Sysetup/Aluminum-boxes/18 x 29 x 47 cms/Parts/Plates and angles/Connector.FCStd

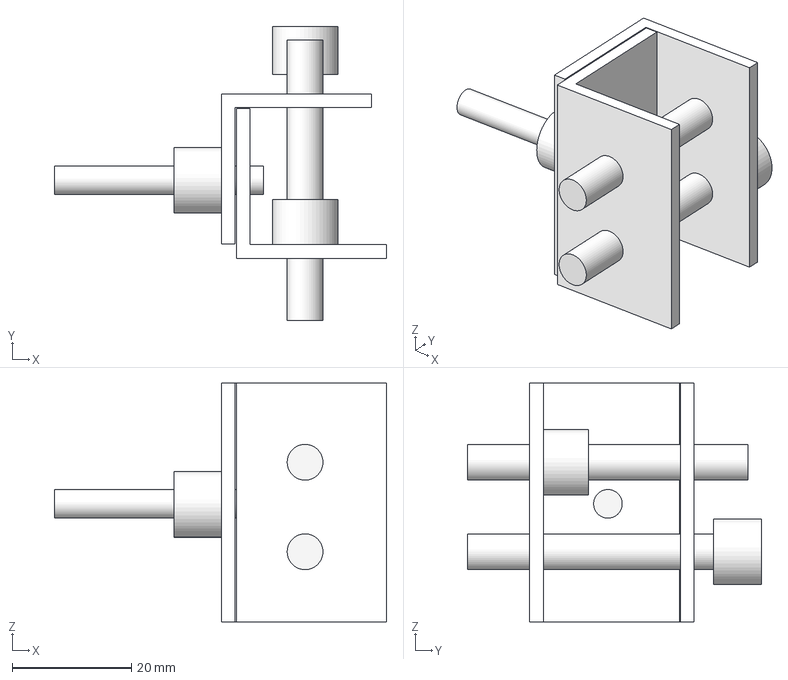
[picture p19: CAD file, 2022-02-21]
18 x 29 x 47 cms/Parts/Plates and angles/Connector.FCStd
55.6 x 49.2 x 40.0 mm
Thickness021
