Sysetup/Aluminum-boxes/18x29x47cms/Parts/Covers/Bottom cover.FCStd

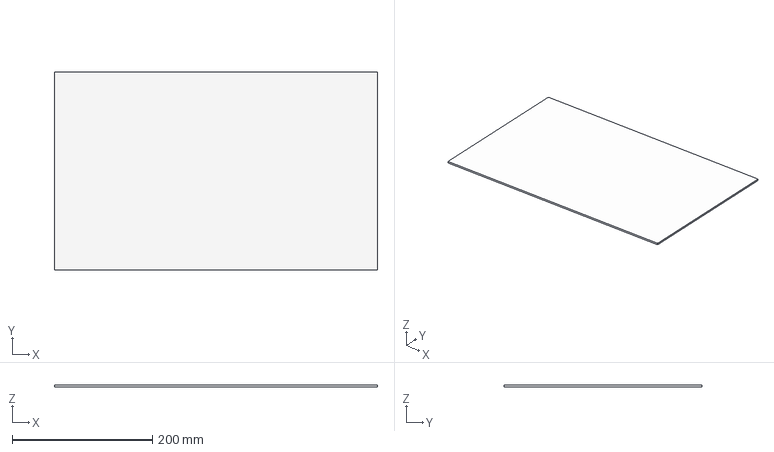
[picture p20: CAD file, 2022-03-06]
18x29x47cms/Parts/Covers/Bottom cover.FCStd
460.0 x 282.0 x 3.00 mm
