Sysetup/Aluminum-boxes/29x29x47cms/Parts/Covers/#21 Left cover.FCStd

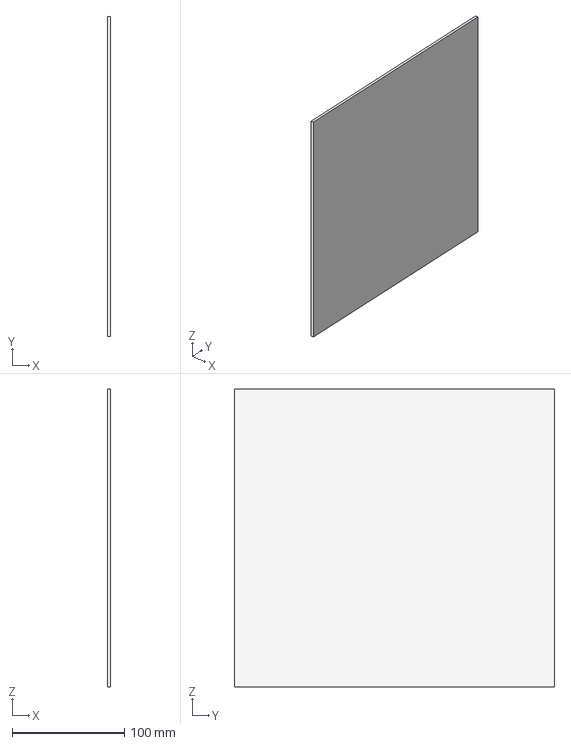
[picture p21: CAD file, 2022-01-28]
29x29x47cms/Parts/Covers/#21 Left cover.FCStd
3.00 x 285.0 x 265.0 mm
