Sysetup/Aluminum-boxes/18x29x47cms/Parts/Covers/Top cover.FCStd

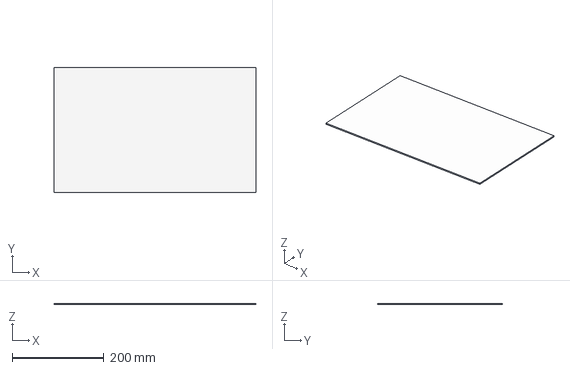
[picture p22: CAD file, 2022-03-06]
18x29x47cms/Parts/Covers/Top cover.FCStd
441.0 x 272.0 x 3.00 mm
