Sysetup/Aluminum-boxes/18 x 29 x 47 cms/Parts/Covers/Left cover.FCStd

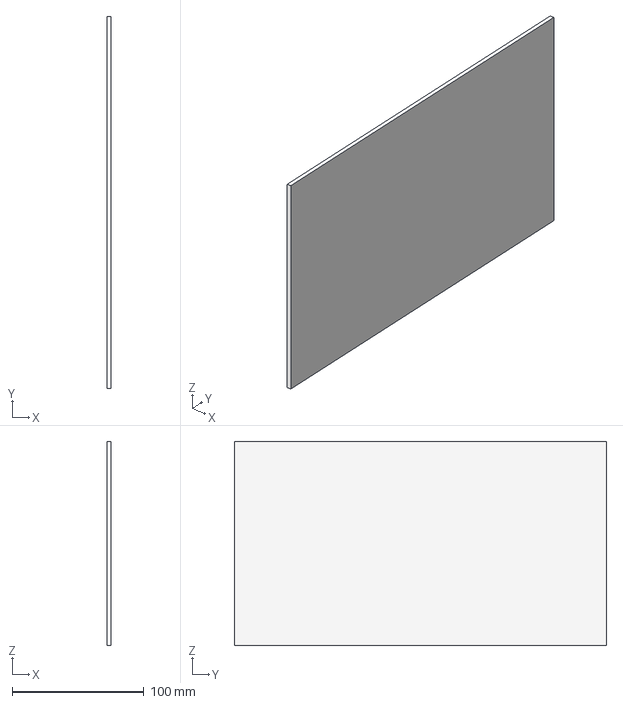
[picture p23: CAD file, 2022-03-06]
18 x 29 x 47 cms/Parts/Covers/Left cover.FCStd
3.00 x 282.0 x 155.0 mm
