Sysetup/Aluminum-boxes/29x29x47cms/Parts/Covers/#17 Front cover.FCStd

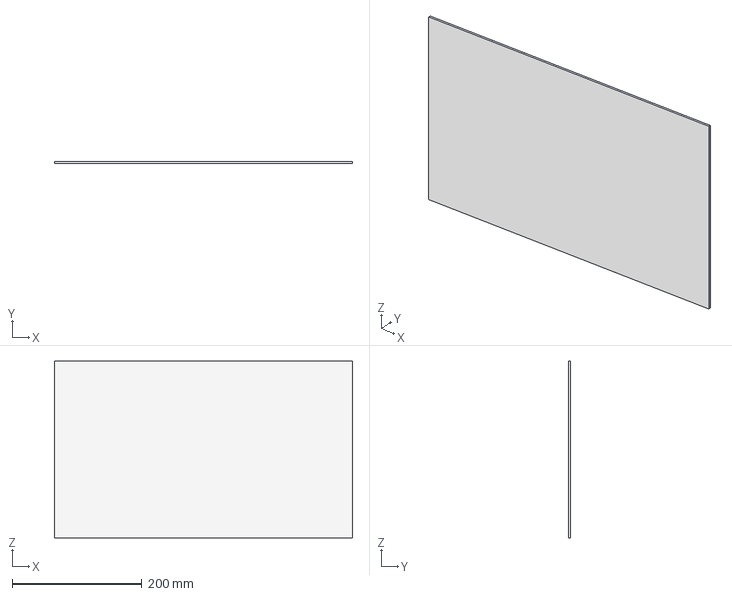
[picture p24: CAD file, 2022-01-28]
29x29x47cms/Parts/Covers/#17 Front cover.FCStd
460.0 x 3.00 x 273.0 mm
