Sysetup/Aluminum-boxes/18 x 29 x 47 cms/Parts/Covers/Alfajor.FCStd

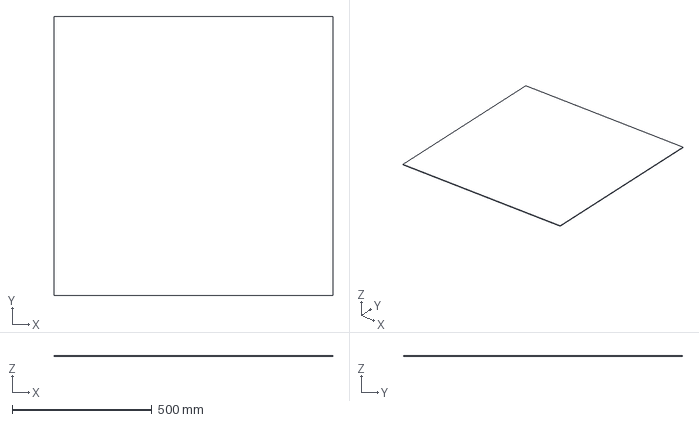
[picture p25: CAD file, 2022-03-06]
18 x 29 x 47 cms/Parts/Covers/Alfajor.FCStd
1000.0 x 1000.0 x 3.00 mm
