Sysetup/Aluminum-boxes/29x29x47cms/Parts/Covers/#18 Top cover.FCStd

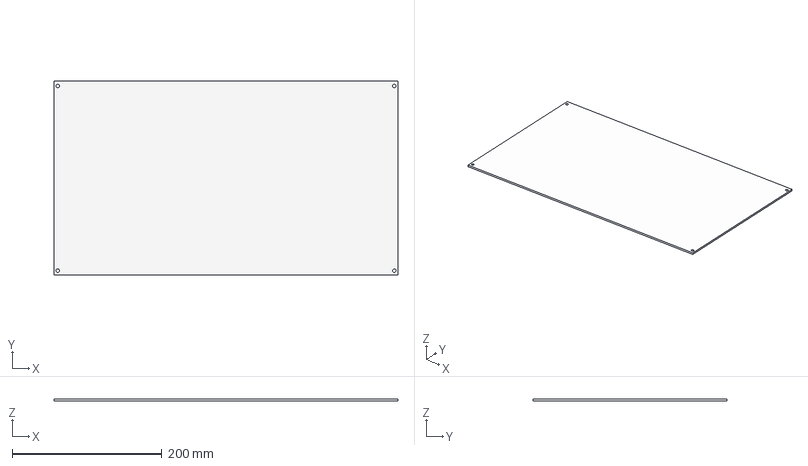
[picture p26: CAD file, 2022-01-28]
29x29x47cms/Parts/Covers/#18 Top cover.FCStd
460.0 x 260.0 x 3.00 mm
